klouderone/SeagullMacropad/Seagull Kicad/Tired Seagull.kicad_sch

## KiCad design Seagull Kicad/Tired Seagull.kicad_sch (2024-05-01)

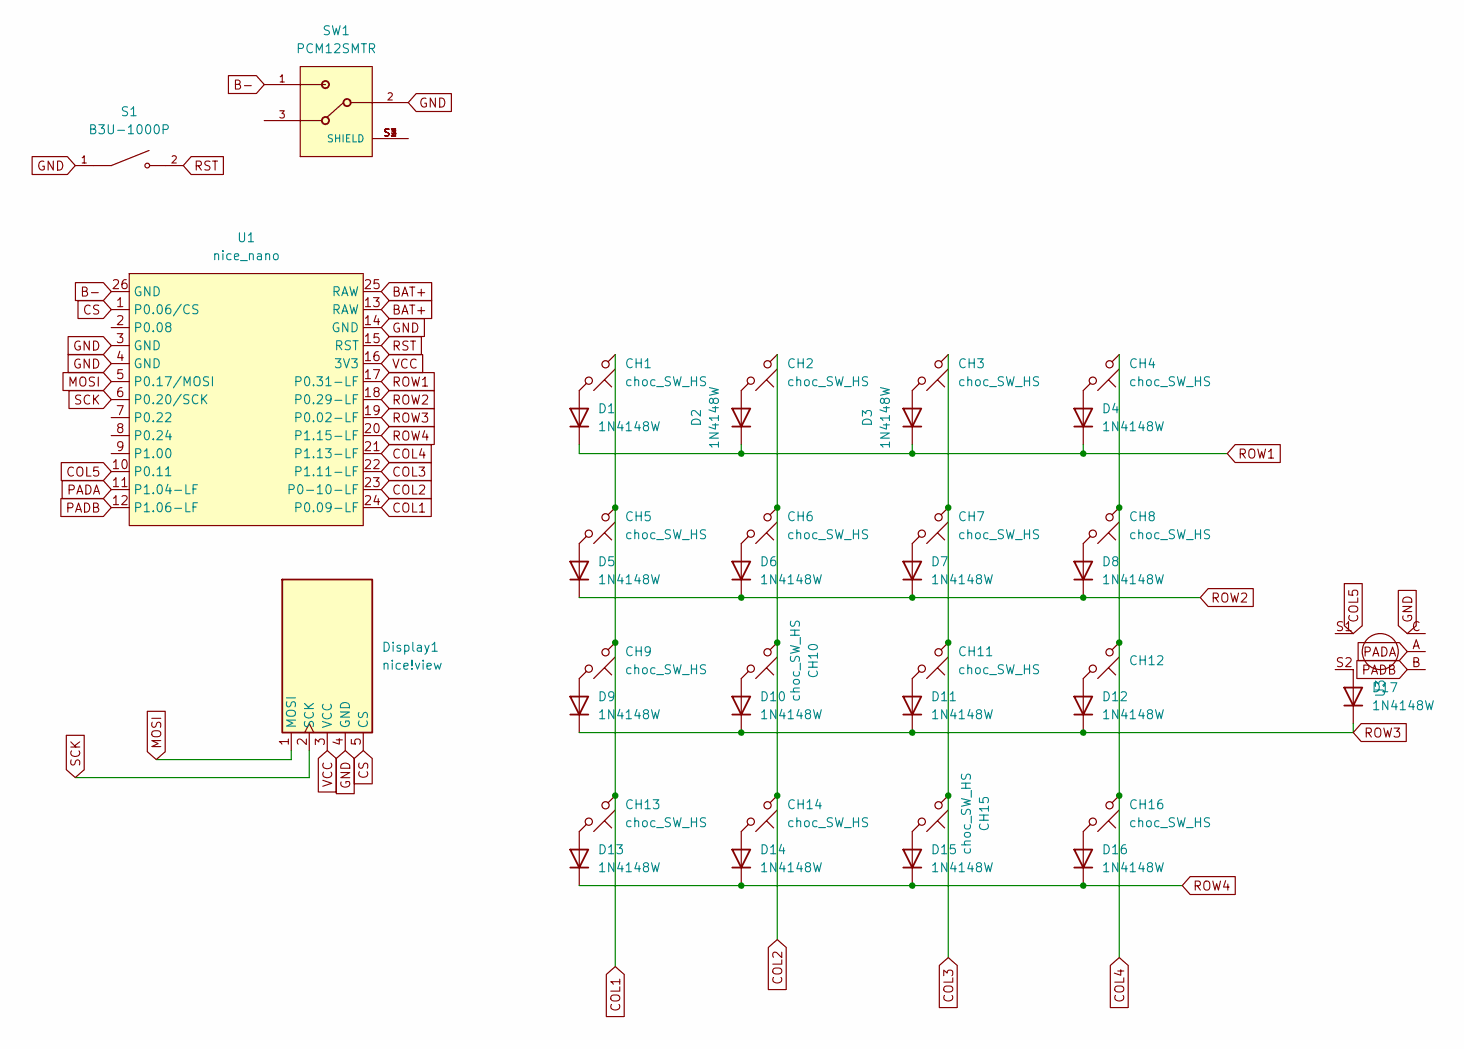
[picture p4: schematic Tired Seagull.kicad_sch]

Parts:
CH1, CH2, CH3, CH4, CH5, CH6, CH7, CH8, CH9, CH10, CH11, CH12, CH13, CH14, CH15, CH16: choc_SW_HS; SW_MXchoc_HS_1u
D1, D2, D3, D4, D5, D6, D7, D8, D9, D10, D11, D12, D13, D14, D15, D16, D17: 1N4148W; D_SOD-123
Display1: nice!view; nice_view
S1: B3U-1000P
SW1: PCM12SMTR; SW_SPDT_PCM12
U1: nice_nano; Universal_Pro_Micro_Footprint
U3: ROT_Alps_EC11E-Switch

Connections:
B-: SW1.1, U1.26 (GND)
BAT+: U1.13 (RAW), U1.25 (RAW)
COL1: CH1.1, CH5.1, CH9.1, CH13.1, U1.24 (P0.09-LF)
COL2: CH2.1, CH6.1, CH10.1, CH14.1, U1.23 (P0-10-LF)
COL3: CH3.1, CH7.1, CH11.1, CH15.1, U1.22 (P1.11-LF)
COL4: CH4.1, CH8.1, CH12.1, CH16.1, U1.21 (P1.13-LF)
COL5: U1.10 (P0.11), U3.S1
CS: Display1.5 (CS), U1.1 (P0.06/CS)
GND: Display1.4 (GND), S1.1, SW1.2, U1.3 (GND), U1.4 (GND), U1.14 (GND), U3.C
MOSI: Display1.1 (MOSI), U1.5 (P0.17/MOSI)
unnamed: CH1.2, D1.2 (A)
unnamed: CH2.2, D2.2 (A)
unnamed: CH3.2, D3.2 (A)
unnamed: CH4.2, D4.2 (A)
unnamed: CH5.2, D5.2 (A)
unnamed: CH6.2, D6.2 (A)
unnamed: CH7.2, D7.2 (A)
unnamed: CH8.2, D8.2 (A)
unnamed: CH9.2, D9.2 (A)
unnamed: CH10.2, D10.2 (A)
unnamed: CH11.2, D11.2 (A)
unnamed: CH12.2, D12.2 (A)
unnamed: CH13.2, D13.2 (A)
unnamed: CH14.2, D14.2 (A)
unnamed: CH15.2, D15.2 (A)
unnamed: CH16.2, D16.2 (A)
unnamed: D17.2 (A), U3.S2
unnamed: SW1.S1 (SHIELD), SW1.S2 (SHIELD), SW1.S3 (SHIELD), SW1.S4 (SHIELD)
PADA: U1.11 (P1.04-LF), U3.A
PADB: U1.12 (P1.06-LF), U3.B
ROW1: D1.1 (K), D2.1 (K), D3.1 (K), D4.1 (K), U1.17 (P0.31-LF)
ROW2: D5.1 (K), D6.1 (K), D7.1 (K), D8.1 (K), U1.18 (P0.29-LF)
ROW3: D9.1 (K), D10.1 (K), D11.1 (K), D12.1 (K), D17.1 (K), U1.19 (P0.02-LF)
ROW4: D13.1 (K), D14.1 (K), D15.1 (K), D16.1 (K), U1.20 (P1.15-LF)
RST: S1.2, U1.15 (RST)
SCK: Display1.2 (SCK), U1.6 (P0.20/SCK)
VCC: Display1.3 (VCC), U1.16 (3V3)
