klouderone/SeagullMacropad/Firmware/Seagull QMK-VIAL Code/keymaps/vial/config.h

/*
Copyright 2021 gkeyboard

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
You should have received a copy of the GNU General Public License
along with this program.  If not, see <http://www.gnu.org/licenses/>.
*/

#pragma once

#define VIAL_KEYBOARD_UID {0x0B, 0x98, 0x18, 0x84, 0xA8, 0x29, 0x6A, 0x03}
#define VIAL_UNLOCK_COMBO_ROWS {0, 0}
#define VIAL_UNLOCK_COMBO_COLS {0, 1}
// #define VIAL_TAP_DANCE_ENTRIES 12

// Connects each switch in the dip switch to the GPIO pin of the MCU
 
#define DIP_SWITCH_PINS { E6 }

// For split keyboards, you can separately define the right side pins
// #define DIP_SWITCH_PINS_RIGHT { ... }
/*
 * Feature disable options
 *  These options are also useful to firmware size reduction.
 */

/* disable debug print */
//#define NO_DEBUG

/* disable print */
//#define NO_PRINT

/* disable action features */
//#define NO_ACTION_LAYER
//#define NO_ACTION_TAPPING
//#define NO_ACTION_ONESHOT

#define OLED_BRIGHTNESS 128
#define OLED_DISPLAY_128x32
